brrastak/furnace/simulations/charge_pump_simulation/charge_pump_simulation.kicad_sch

## KiCad design simulations/charge_pump_simulation/charge_pump_simulation.kicad_sch (2025-03-29)

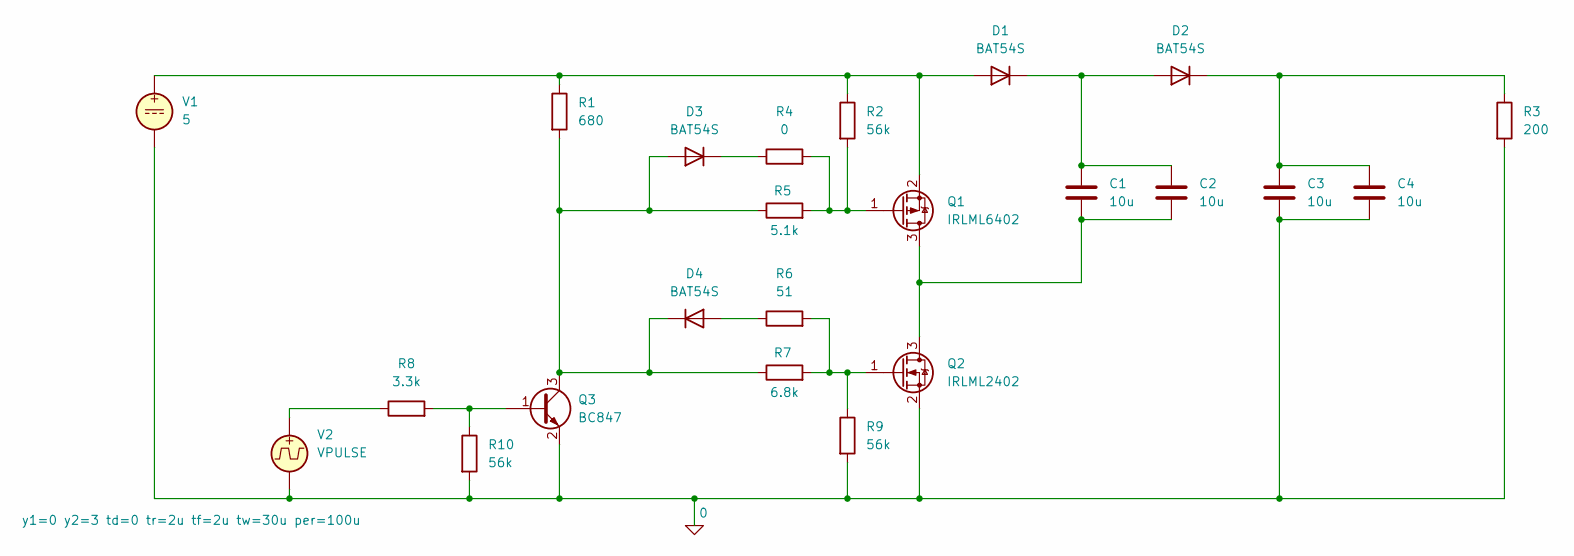
[picture p57: schematic charge_pump_simulation.kicad_sch]

Parts:
C1, C2, C3, C4: 10u
D1, D2, D3, D4: BAT54S
Q1: IRLML6402; SOT-23
Q2: IRLML2402; SOT-23
Q3: BC847; SOT-23
R1: 680
R2, R9, R10: 56k
R3: 200
R4: 0
R5: 5.1k
R6: 51
R7: 6.8k
R8: 3.3k
V1: 5
V2: VPULSE

Connections:
0: C3.2, C4.2, Q2.2 (S), Q3.2 (E), R3.2, R9.2, R10.2, V1.2, V2.2
unnamed: C1.1, C2.1, D1.1 (K), D2.2 (A)
unnamed: C1.2, C2.2, Q1.3 (D), Q2.3 (D)
unnamed: C3.1, C4.1, D2.1 (K), R3.1
unnamed: D1.2 (A), Q1.2 (S), R1.1, R2.1, V1.1
unnamed: D3.1 (K), R4.1
unnamed: D3.2 (A), D4.1 (K), Q3.3 (C), R1.2, R5.1, R7.1
unnamed: D4.2 (A), R6.1
unnamed: Q1.1 (G), R2.2, R4.2, R5.2
unnamed: Q2.1 (G), R6.2, R7.2, R9.1
unnamed: Q3.1 (B), R8.2, R10.1
unnamed: R8.1, V2.1
