brrastak/furnace/furnace_controller_FW/src/bsp.rs

use display_interface_i2c::I2CInterface;
pub use stm32f1xx_hal as hal;
pub use hal:: {
        afio::spi2,
        prelude::*,
        rcc::*,
        gpio::*,
        i2c::{self, BlockingI2c, DutyCycle},
        pac::Peripherals,
        spi::{self, Spi, Phase, Polarity},
        time::ms,
        timer::{Channel, Timer, Tim2NoRemap},
        serial::{self, Rx},
        watchdog::IndependentWatchdog,
    };
pub use ssd1309::{prelude::*, Builder};

pub use crate::keyboard::*;
use crate::safe_panic::copy_safe_pin;


/// Number of thermocouples
pub const TEMP_NUM: usize = 5;
/// Number of bytes in each packet received from the 230V board
pub const RX_DATA_LEN: usize = 22;

/// Possible error while receiving the 230V board data
#[derive(Debug, PartialEq)]
pub enum Board230Error {
    UartError,
    CrcError,
    ParseError,
    NoTempValue,
}

/// Structure containing 230V board data
#[derive(Debug, PartialEq)]
pub struct RxData {
    /// RMS grid voltage value in V
    pub voltage: u16,
    /// RMS load current value in 0.1A
    pub current: u16,
    /// Triac temperature value in Celsius degree
    pub triac_temp: i16,
}


pub type OledDisplay = GraphicsMode<I2CInterface<BlockingI2c<hal::pac::I2C1>>>;
pub type DigitalOutput = ErasedPin<Output>;
pub type TempSpi = Spi<hal::pac::SPI2, u8, PullUp>;
pub type Board230Rx = Rx<hal::pac::USART2>;

pub struct Board {
    pub rcc: Rcc,
    pub oled: OledDisplay,
    pub heater_control: &'static mut DigitalOutput,
    pub buzzer: DigitalOutput,
    pub keyboard: Keyboard,
    pub watchdog: IndependentWatchdog,
    pub temp_select: [DigitalOutput; 5],
    pub temp_spi: TempSpi,
    pub board230_rx: Board230Rx,
}

impl Board {

    pub fn new(p: Peripherals) -> Self {

        let mut flash = p.FLASH.constrain();
        let mut rcc = p.RCC.freeze(
            Config::hse(8.MHz()).sysclk(72.MHz()).pclk1(36.MHz()).pclk2(72.MHz()),
            &mut flash.acr,
        );
        let mut afio = p.AFIO.constrain(&mut rcc);

        let mut gpioa = p.GPIOA.split(&mut rcc);
        let mut gpiob = p.GPIOB.split(&mut rcc);

        let (pa15, pb3, pb4) = afio.mapr.disable_jtag(gpioa.pa15, gpiob.pb3, gpiob.pb4);

        // Discrete outputs
        let heater_control = copy_safe_pin(
            gpioa.pa2.into_push_pull_output_with_state(&mut gpioa.crl, PinState::Low).erase()
        );
        let mut display_power_en = gpiob.pb8.into_push_pull_output(&mut gpiob.crh).erase();
        let buzzer = pa15.into_push_pull_output_with_state(&mut gpioa.crh, PinState::Low).erase();

        // Keyboard
        let keyboard_rows = [
            gpioa.pa8.into_floating_input(&mut gpioa.crh).erase(),
            gpioa.pa9.into_floating_input(&mut gpioa.crh).erase(),
            gpioa.pa10.into_floating_input(&mut gpioa.crh).erase(),
            gpioa.pa11.into_floating_input(&mut gpioa.crh).erase(),
            gpioa.pa12.into_floating_input(&mut gpioa.crh).erase(),
        ];
        let keyboard_cols = [
            pb4.into_open_drain_output_with_state(&mut gpiob.crl, PinState::High).erase(),
            gpiob.pb5.into_open_drain_output_with_state(&mut gpiob.crl, PinState::High).erase(),
            gpiob.pb9.into_open_drain_output_with_state(&mut gpiob.crh, PinState::High).erase(),
            gpioa.pa0.into_open_drain_output_with_state(&mut gpioa.crl, PinState::High).erase(),
        ];
        let keyboard = Keyboard::new(keyboard_rows, keyboard_cols);

        // Charge pump clock
        let charge_pump_clk = gpioa.pa1.into_alternate_push_pull(&mut gpioa.crl);
        let mut pwm = p.TIM2
            .pwm_hz::<Tim2NoRemap, _, _>(charge_pump_clk, &mut afio.mapr, 10.kHz(), &mut rcc);
        pwm.enable(Channel::C2);
        pwm.set_duty(Channel::C2, pwm.get_max_duty() / 3);

        // OLED display
        let mut display_reset = pb3.into_push_pull_output(&mut gpiob.crl);
        let display_i2c_clk = gpiob.pb6.into_alternate_open_drain(&mut gpiob.crl);
        let display_i2c_sda = gpiob.pb7.into_alternate_open_drain(&mut gpiob.crl);
        display_power_en.set_high();
        let mut display_delay = p.TIM4.delay_us(&mut rcc);
        let display_i2c = BlockingI2c::new(
            p.I2C1,
            (display_i2c_clk, display_i2c_sda),
            i2c::Mode::Fast {
                frequency: 100u32.kHz(),
                duty_cycle: DutyCycle::Ratio2to1,
            },
            &mut rcc,
            1000,
            10,
            1000,
            1000,
        );
        let i2c_interface = I2CInterface::new(display_i2c, 0x3C, 0x40);
        let mut oled: GraphicsMode<_> = Builder::new()
            .with_rotation(DisplayRotation::Rotate180)
            .connect(i2c_interface)
            .into();
        oled.reset(&mut display_reset, &mut display_delay).unwrap();

        // SPI for thermocouples
        let temp_spi_cs0 = gpiob.pb10.into_push_pull_output_with_state(&mut gpiob.crh, PinState::High).erase();
        let temp_spi_cs1 = gpiob.pb11.into_push_pull_output_with_state(&mut gpiob.crh, PinState::High).erase();
        let temp_spi_cs2 = gpiob.pb1.into_push_pull_output_with_state(&mut gpiob.crl, PinState::High).erase();
        let temp_spi_cs3 = gpiob.pb2.into_push_pull_output_with_state(&mut gpiob.crl, PinState::High).erase();
        let temp_spi_cs4 = gpiob.pb15.into_push_pull_output_with_state(&mut gpiob.crh, PinState::High).erase();
        let temp_select = [temp_spi_cs0, temp_spi_cs1, temp_spi_cs2, temp_spi_cs3, temp_spi_cs4];
        assert_eq!(temp_select.len(), TEMP_NUM);
        let temp_spi_clk = gpiob.pb13.into_alternate_push_pull(&mut gpiob.crh);
        let temp_spi_miso = gpiob.pb14.into_pull_up_input(&mut gpiob.crh);
        let temp_spi = Spi::new(
            p.SPI2,
            (Some(temp_spi_clk), Some(temp_spi_miso), None::<spi2::Mo>),
            spi::Mode{polarity: Polarity::IdleLow, phase: Phase::CaptureOnFirstTransition},
            2.MHz(),
            &mut rcc
        );

        // UART to receive data from the 230V board
        let rx_pin = gpioa.pa3.into_floating_input(&mut gpioa.crl);
        let board230_rx = p.USART2.rx(
            rx_pin,
            serial::Config::default()
                .baudrate(9600.bps())
                .wordlength_8bits()
                .parity_none()
                .stopbits(serial::StopBits::STOP1),
            &mut rcc
        );

        let mut watchdog = IndependentWatchdog::new(p.IWDG);
        watchdog.start(3000.millis());


        Board {
            rcc,
            oled,
            heater_control,
            buzzer,
            keyboard,
            watchdog,
            temp_select,
            temp_spi,
            board230_rx,
        }
    }
}
